GEI-duo/UCES_project/UCES_project/src/operation-base/src/controllers/ButtonController.cpp

#include <Arduino.h>
#include <OneButton.h>
#include "config.h"

OneButton button(BUTTON_PIN, true);  // true -> pull-down externally

void setupButton(void (*clickHandler)()) {
  button.attachClick(clickHandler);
}

void loopButton() {
  button.tick();
}

void buttonTask(void* pvParameters) {
  while (true) {
    loopButton();
  }
}
