GEI-duo/UCES_project/UCES_project/src/operation-base/include/melody.h

#ifndef MELODY_H
#define MELODY_H

// Include pitches if needed
#include "pitches.h"

// Define melody notes and durations
extern int melody[];
extern int durations[];
extern const int melody_size;

#endif // MELODY_H
