GEI-duo/UCES_project/UCES_project/src/operation-base/examples/arduino/all/LEDController.cpp

#include "LEDController.h"
#include "Config.h"

void  setupLED() {
  pinMode(LED_PIN, OUTPUT);
}

void handleLEDMessage(const String& message) {
  if (message == "ON") {
    digitalWrite(LED_PIN, HIGH);
  } else if (message == "OFF") {
    digitalWrite(LED_PIN, LOW);
  }
}
