GEI-duo/UCES_project/UCES_project/src/operation-base/examples/idf/wifi/main.c

#include "esp_err.h"
#include "esp_event.h"
#include "esp_log.h"
#include "esp_netif.h"
#include "esp_system.h"
#include "esp_wifi.h"
#include "freertos/FreeRTOS.h"
#include "freertos/task.h"
#include "nvs_flash.h"
#include "string.h"

#define WIFI_SSID "Redmi Note 11S"  // Replace with your WiFi SSID
#define WIFI_PASS "0123456789"      // Replace with your WiFi password

static const char* TAG = "WiFi_HelloWorld";

void wifi_event_handler(void* arg, esp_event_base_t event_base,
                        int32_t event_id, void* event_data) {
  if (event_base == WIFI_EVENT && event_id == WIFI_EVENT_STA_START) {
    esp_wifi_connect();
  } else if (event_base == WIFI_EVENT &&
             event_id == WIFI_EVENT_STA_DISCONNECTED) {
    esp_wifi_connect();
    ESP_LOGI(TAG, "retrying connection...");
  } else if (event_base == IP_EVENT && event_id == IP_EVENT_STA_GOT_IP) {
    ip_event_got_ip_t* event = (ip_event_got_ip_t*)event_data;
    ESP_LOGI(TAG, "got IP: " IPSTR, IP2STR(&event->ip_info.ip));
  }
}

void wifi_init_sta() {
  esp_netif_init();
  esp_event_loop_create_default();
  esp_netif_create_default_wifi_sta();

  wifi_init_config_t cfg = WIFI_INIT_CONFIG_DEFAULT();
  esp_wifi_init(&cfg);

  esp_event_handler_instance_t instance_any_id;
  esp_event_handler_instance_t instance_got_ip;
  esp_event_handler_instance_register(WIFI_EVENT, ESP_EVENT_ANY_ID,
                                      &wifi_event_handler, NULL,
                                      &instance_any_id);
  esp_event_handler_instance_register(IP_EVENT, IP_EVENT_STA_GOT_IP,
                                      &wifi_event_handler, NULL,
                                      &instance_got_ip);

  wifi_config_t wifi_config = {
      .sta =
          {
              .ssid = WIFI_SSID,
              .password = WIFI_PASS,
          },
  };

  esp_wifi_set_mode(WIFI_MODE_STA);
  esp_wifi_set_config(ESP_IF_WIFI_STA, &wifi_config);
  esp_wifi_start();

  ESP_LOGI(TAG, "WiFi initialization completed.");
}

void app_main() {
  esp_err_t ret = nvs_flash_init();
  if (ret == ESP_ERR_NVS_NO_FREE_PAGES ||
      ret == ESP_ERR_NVS_NEW_VERSION_FOUND) {
    ESP_ERROR_CHECK(nvs_flash_erase());
    ret = nvs_flash_init();
  }
  ESP_ERROR_CHECK(ret);

  ESP_LOGI(TAG, "ESP32 WiFi Hello World");

  wifi_init_sta();
}
