GEI-duo/UCES_project/UCES_project/src/operation-base/examples/arduino/all/WiFiManager.cpp

#include <WiFi.h>
#include "Config.h"

void setupWiFi() {
  Serial.print("Connecting to WiFi...");

  WiFi.begin(WIFI_SSID, WIFI_PASSWORD);

  while (WiFi.status() != WL_CONNECTED) {
    delay(1000);
    Serial.print(".");
  }
  Serial.println("\nConnected to WiFi!");
}
